jonthomasson/CodeStackOrnament2023/pics/board-front-copper.PNG

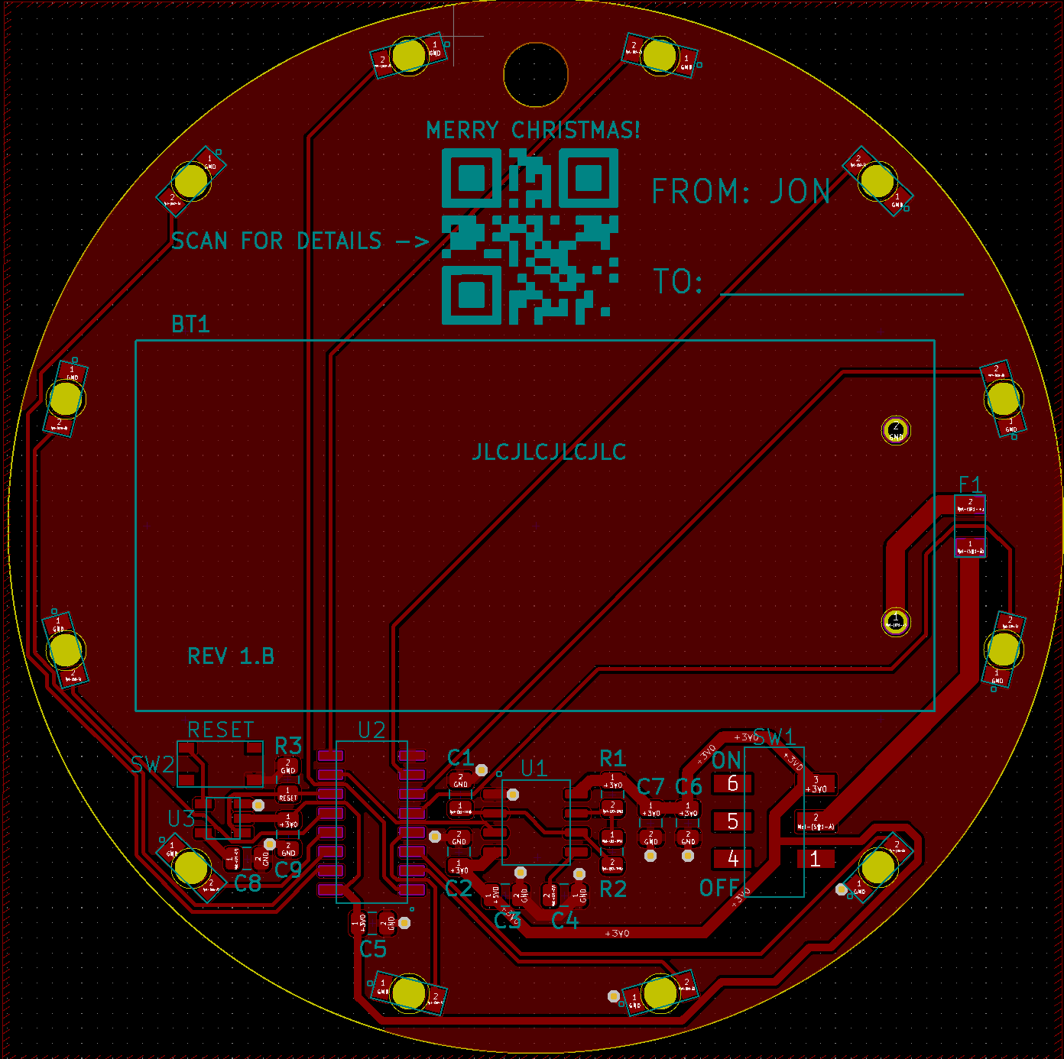
pics/board-front-copper.PNG
