jonthomasson/CodeStackOrnament2023/pics/codestack.png

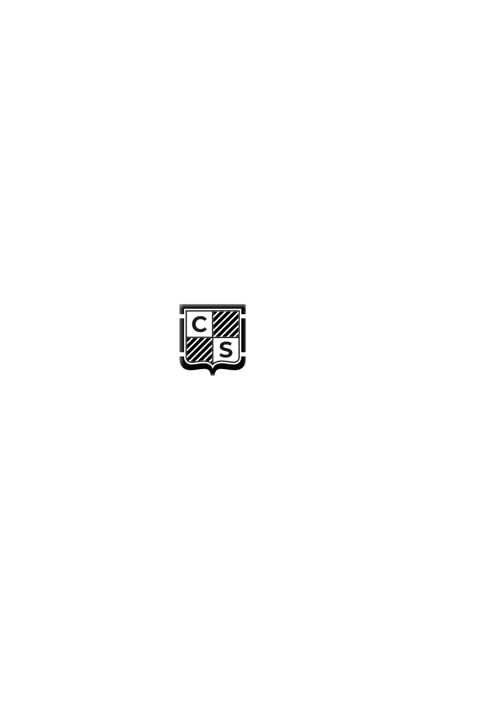
pics/codestack.png
