jonthomasson/CodeStackOrnament2023/pics/g896.png

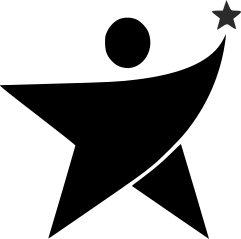
pics/g896.png
