jonthomasson/CodeStackOrnament2023/pics/g918.png

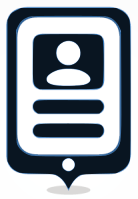
pics/g918.png
