jonthomasson/CodeStackOrnament2023/pics/g968.png

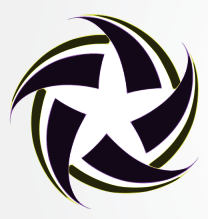
pics/g968.png
