jonthomasson/CodeStackOrnament2023/pics/g1731.png

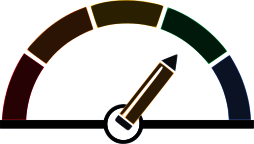
pics/g1731.png
