jonthomasson/CodeStackOrnament2023/pics/path858.png

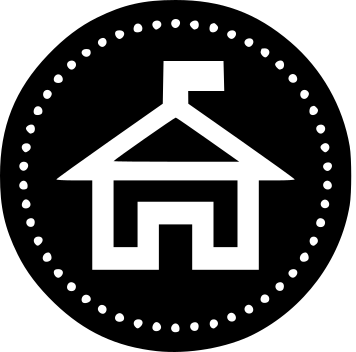
pics/path858.png
