jonthomasson/CodeStackOrnament2023/pics/path877.png

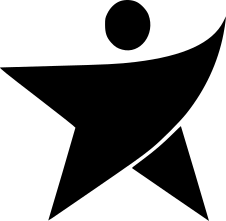
pics/path877.png
