jonthomasson/CodeStackOrnament2023/pics/path1424.png

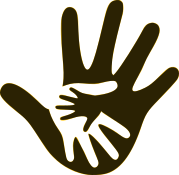
pics/path1424.png
