jonthomasson/CodeStackOrnament2023/pics/simulator.PNG

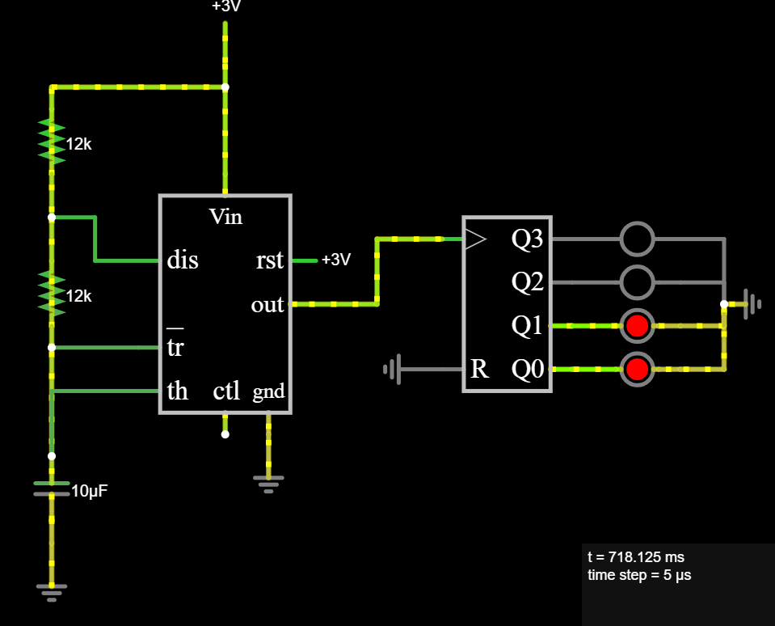
pics/simulator.PNG
